newdigate/samd21g-midi-tool/docs/assembly-top.JPG

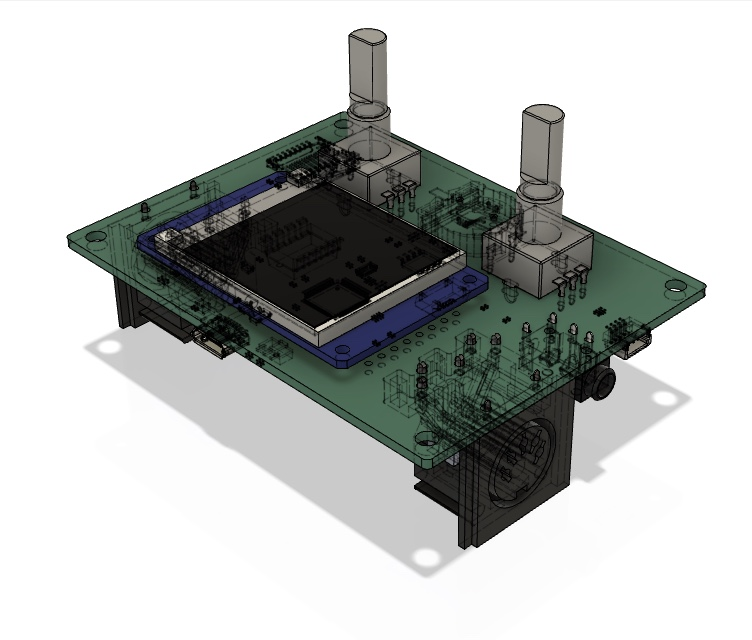
docs/assembly-top.JPG
